dchwebb/Oscar/Graphics/lcd1.webp

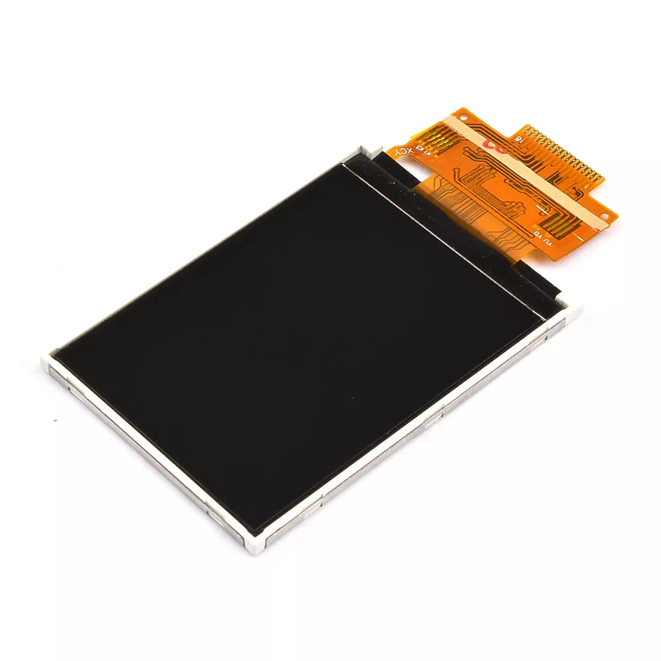
Graphics/lcd1.webp
