dchwebb/Oscar/Graphics/lcd2.webp

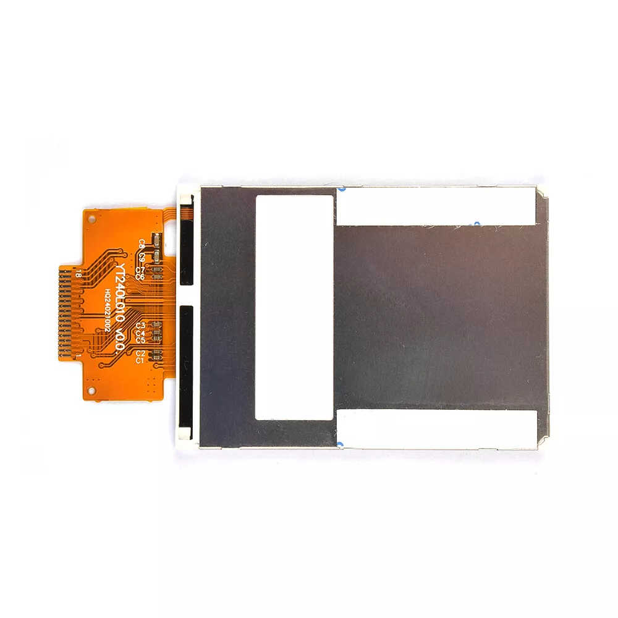
Graphics/lcd2.webp
