dchwebb/Oscar/Graphics/Midi1.jpg

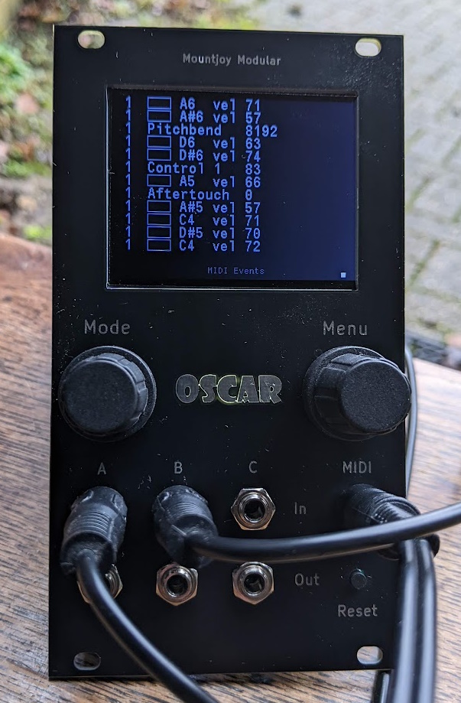
Graphics/Midi1.jpg
