dchwebb/Oscar/Graphics/Midi2.jpg

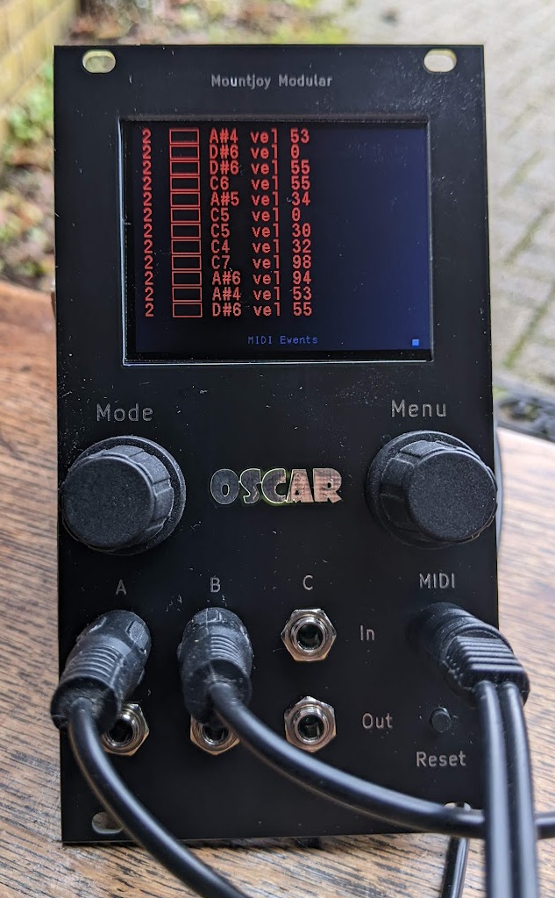
Graphics/Midi2.jpg
