dchwebb/Oscar/Graphics/midi_v3.jpg

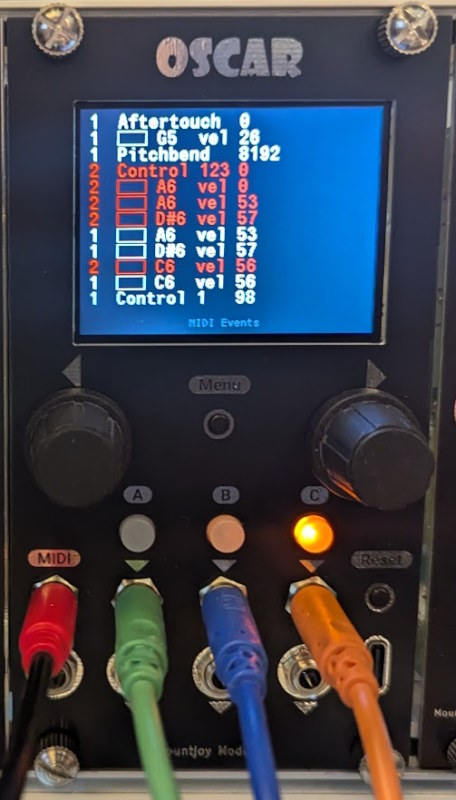
Graphics/midi_v3.jpg
