dchwebb/Oscar/Graphics/nav1.jpg

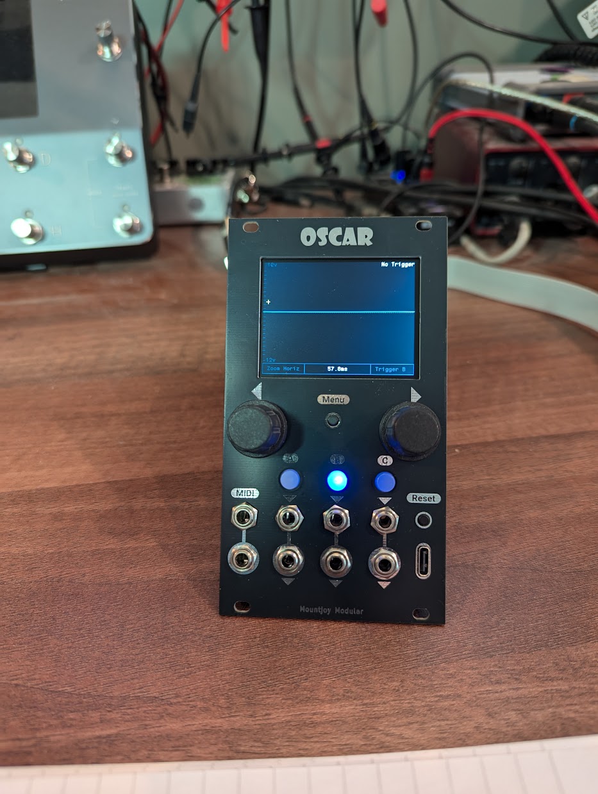
Graphics/nav1.jpg
