dchwebb/Oscar/Graphics/Osc_v3.jpg

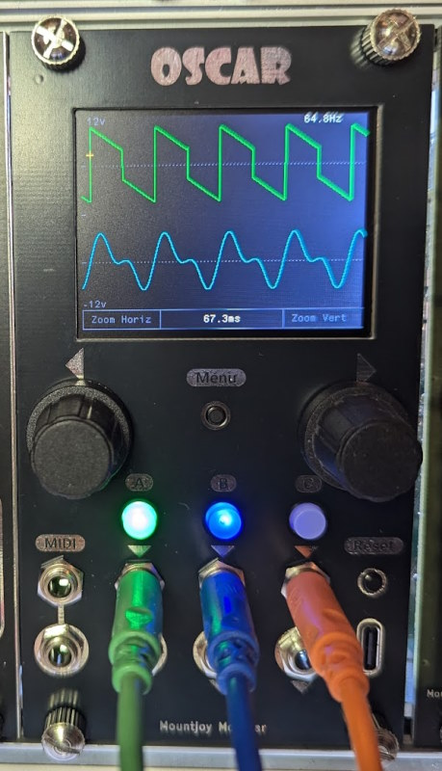
Graphics/Osc_v3.jpg
