dchwebb/Oscar/Graphics/OscA.jpg

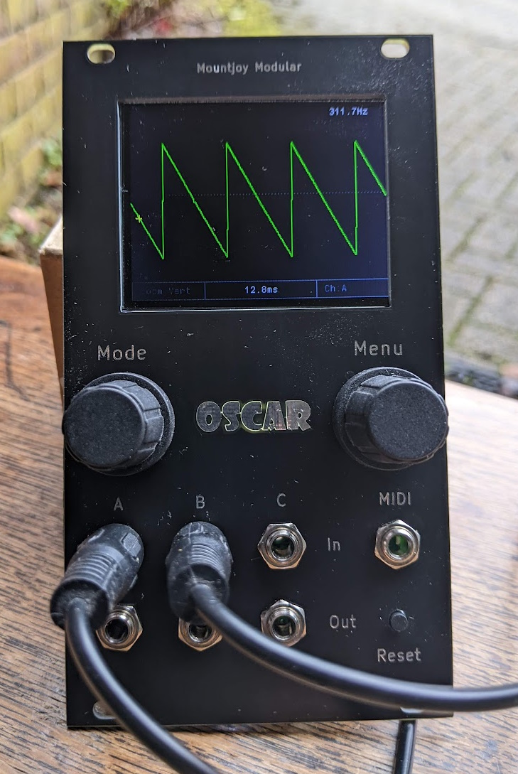
Graphics/OscA.jpg
