dchwebb/Oscar/Graphics/OscAB.jpg

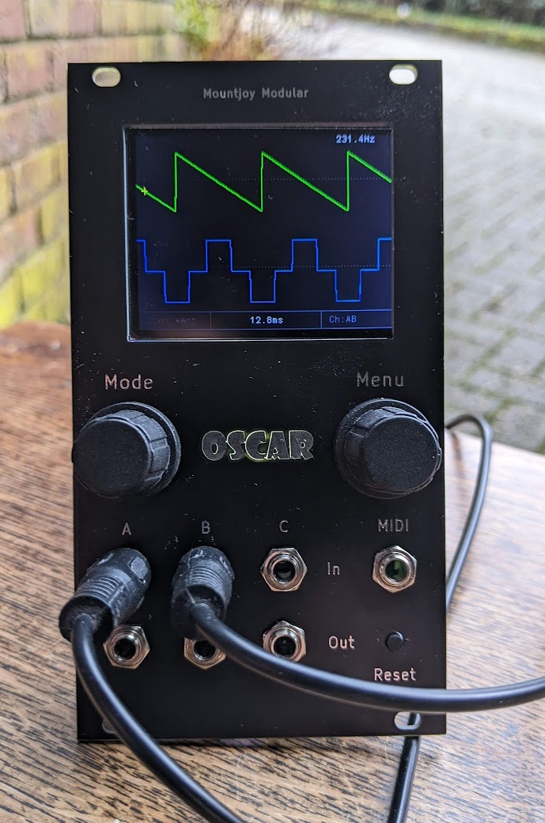
Graphics/OscAB.jpg
