dchwebb/Oscar/Graphics/tuner_v3.jpg

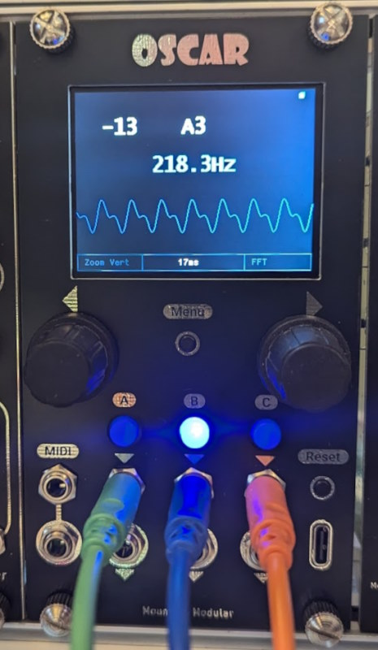
Graphics/tuner_v3.jpg
