dchwebb/Oscar/Graphics/waterfall_v3.jpg

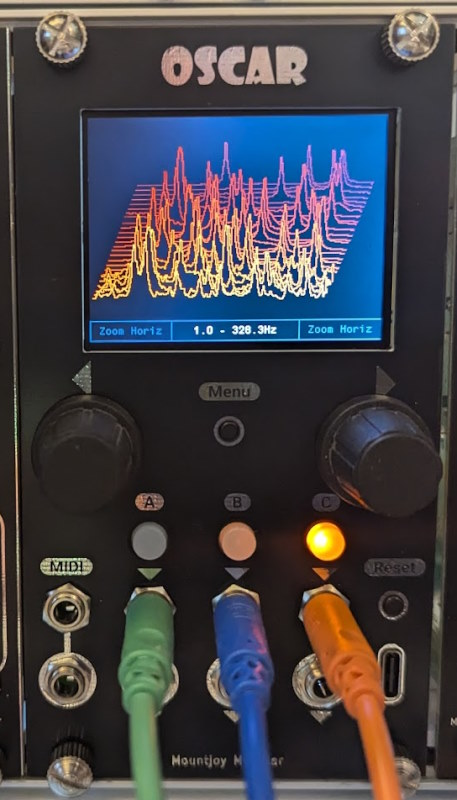
Graphics/waterfall_v3.jpg
