dchwebb/Oscar/Graphics/WaterfallA.jpg

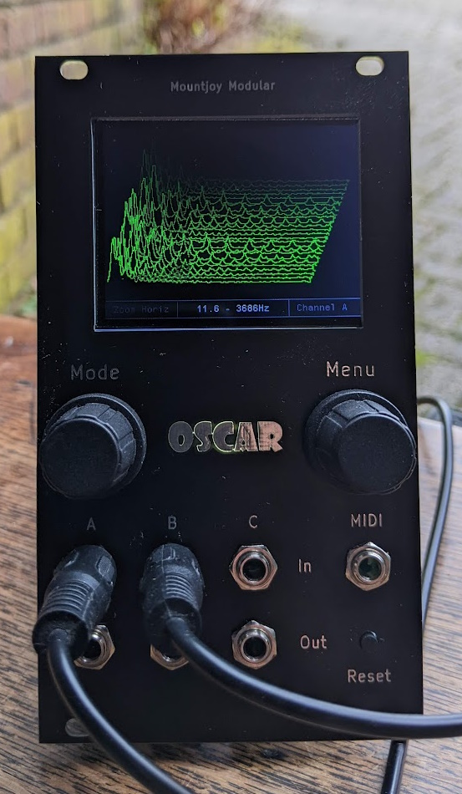
Graphics/WaterfallA.jpg
