dchwebb/Oscar/Graphics/WaterfallB.jpg

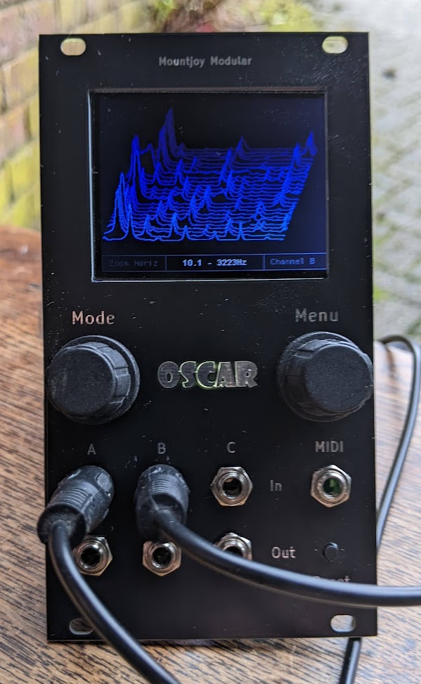
Graphics/WaterfallB.jpg
