dchwebb/Oscar/Graphics/construction1.jpg

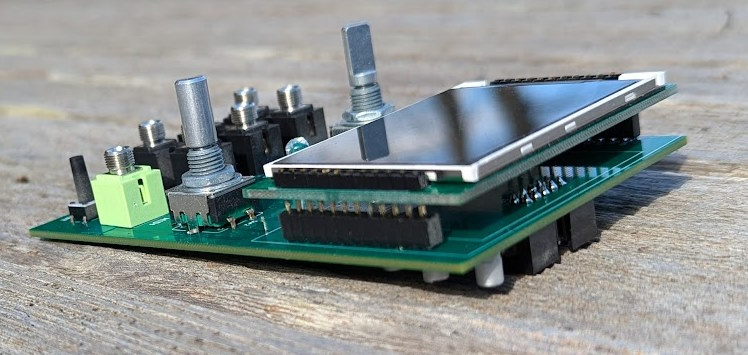
Graphics/construction1.jpg
