dchwebb/Oscar/Graphics/construction2.jpg

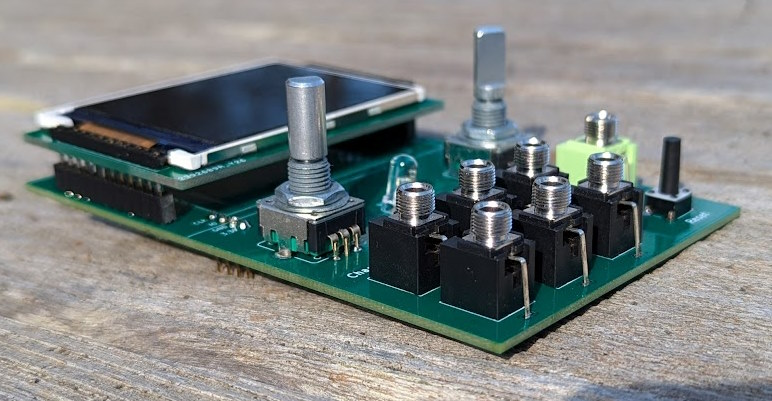
Graphics/construction2.jpg
