dchwebb/Oscar/Graphics/construction3.jpg

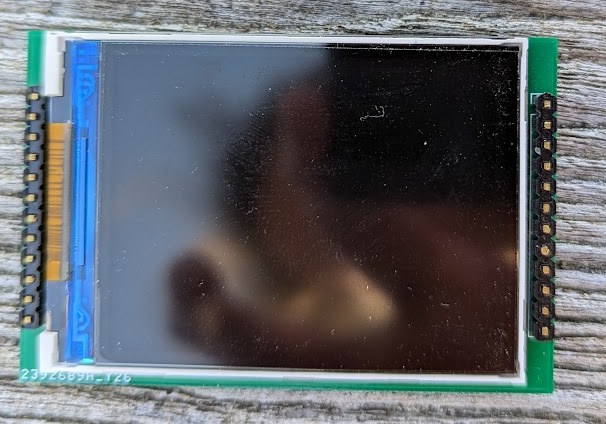
Graphics/construction3.jpg
