dchwebb/Oscar/Graphics/construction4.jpg

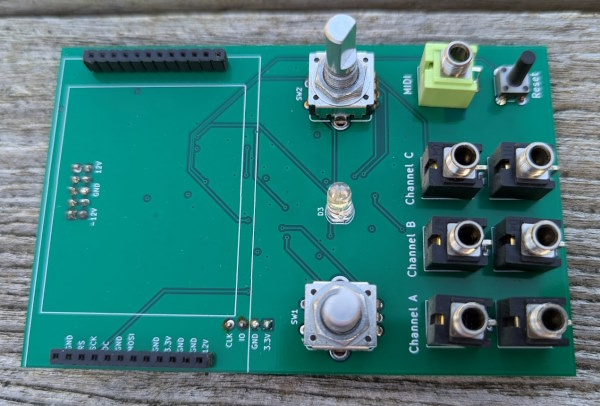
Graphics/construction4.jpg
